openmusictools/mixtee/hardware/pcbs/io/architecture.md

# IO Board — Architecture

## USB Host Hub

- FE1.1s discrete USB 2.0 hub IC (~$1.50, SSOP-28)
- 1 upstream port from Teensy USB host pins (D+/D-) via Main-IO FFC
- 2 downstream ports to panel-mount USB-A sockets
- External 12 MHz crystal + 2x 15 pF load capacitors
- Self-powered configuration (VBUS from 5V_DIG via FFC)
- Per-port VBUS power switching: 2x TPS2051 load switches (500 mA each)
- TPS2051 fault output routed to Teensy GPIO for firmware OC notification
- Minimal external components: crystal, caps, pull-up/pull-down resistors per datasheet

## MIDI IN Circuit

- 3.5mm TRS Type A input with 6N138 optocoupler (DIP-8)
- Input side: 220-ohm series resistor + 1N4148 protection diode across LED
- TRS wiring (Type A): Tip = current sink (pin 5), Ring = current source (pin 4), Sleeve = shield
- Optocoupler output: open-collector, pulled up to 3.3V via 470-ohm
- Output routes via FFC pin 9 (MIDI_RX) to Teensy Serial3 RX (pin 15) at 31.25 kbaud
- 3.5mm TRS compact and modern; legacy 5-pin DIN connects via adapter cable

## MIDI OUT Circuit

- 3.5mm TRS Type A output
- TRS wiring (Type A): Tip = current sink (pin 5), Ring = current source (pin 4), Sleeve = shield
- MIDI_TX arrives from Teensy Serial4 TX (pin 17) via FFC pin 10
- Resistor network: 3.3V -> 10-ohm -> TRS Ring (source); TRS Tip -> 33-ohm -> MIDI_TX
- Standard MIDI current-loop output at 31.25 kbaud
- No optocoupler on output side (receiver's responsibility)

## Ethernet Section

- RJ45 MagJack with integrated magnetics + optional activity LEDs
- Signals arrive via 6-pin ribbon cable (NOT the FFC)
- Post-PHY analog signals -- no impedance-controlled routing required
- No external coupling caps needed — MagJack integrated magnetics provide DC blocking
- Native Teensy 4.1 Ethernet (DP83825I PHY on board), 10/100 Mbps

## Design Notes

- 2-layer PCB sufficient — only USB Full-Speed (12 Mbps) and post-PHY Ethernet analog
- No high-speed digital traces on this board
- Headphone amp has been moved to a standalone **PHONEE** module in the isolated analog domain — see [`../hp/README.md`](../hp/README.md)
- Functional zones: USB section (top), MIDI section (center), FFC/header (interior edge)

---
Back to [README.md](README.md)
